tompany/BCD-0o27-3D-Printables/STL files/ANYCOLUR___bcPositionBlockRight.stl

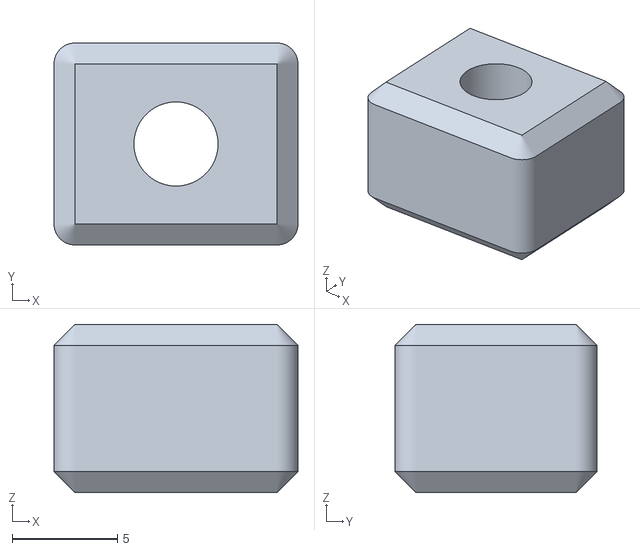
[picture p13: CAD file, 2023-10-08]
STL files/ANYCOLUR___bcPositionBlockRight.stl
11.6 x 9.60 x 8.00
