tompany/BCD-0o27-3D-Printables/STL files/RED___bmRedButtonB.stl

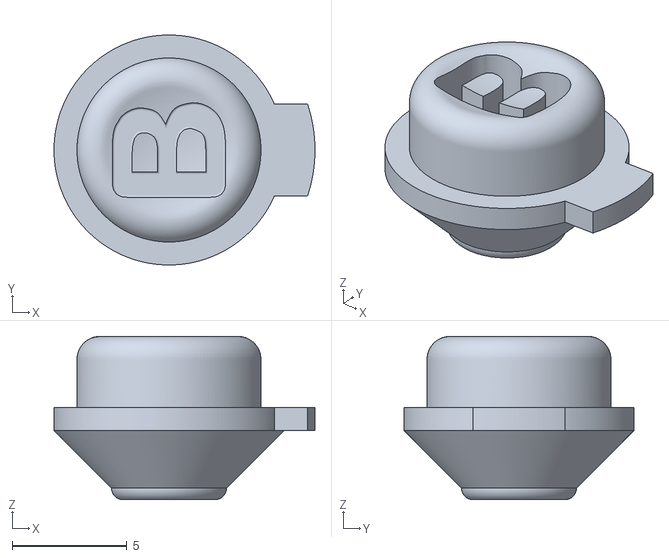
[picture p14: CAD file, 2023-10-08]
STL files/RED___bmRedButtonB.stl
11.3 x 10.00 x 7.10
