tompany/BCD-0o27-3D-Printables/STL files/BLACK___bmBlackButtonLeverW.stl

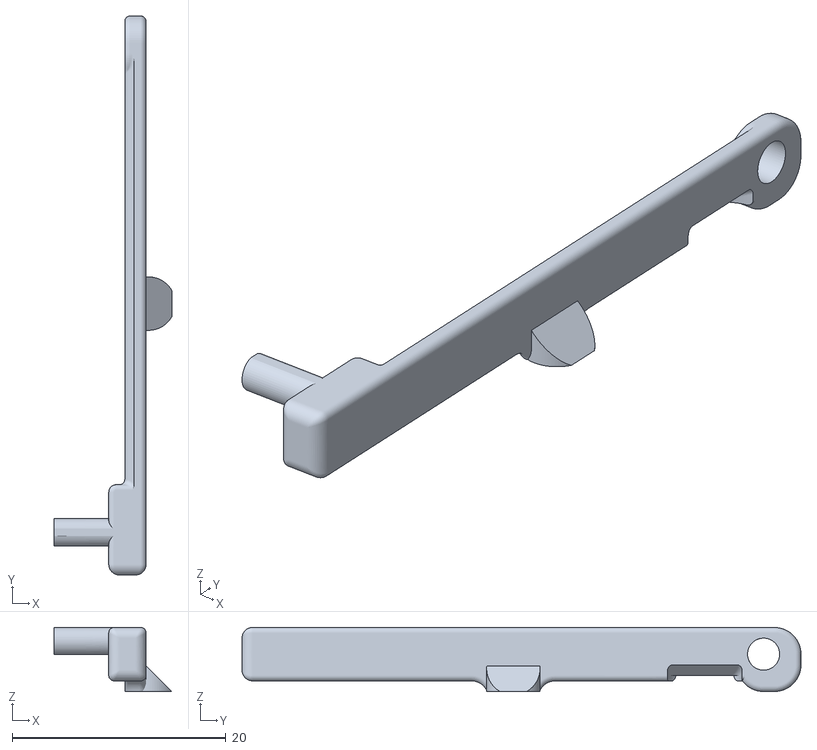
[picture p15: CAD file, 2023-10-08]
STL files/BLACK___bmBlackButtonLeverW.stl
11.0 x 52.3 x 6.00
