tompany/BCD-0o27-3D-Printables/STL files/BLACK___bcSwitchCoverRight.stl

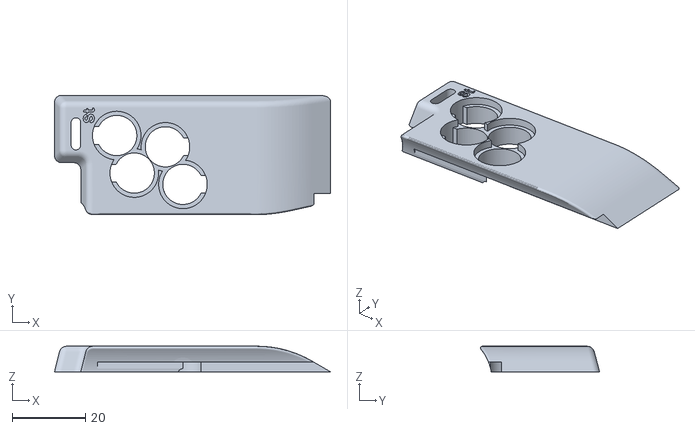
[picture p16: CAD file, 2023-10-08]
STL files/BLACK___bcSwitchCoverRight.stl
75.6 x 32.7 x 7.00
