tompany/BCD-0o27-3D-Printables/STL files/BLUE_TRANSP___bcCoverBot.stl

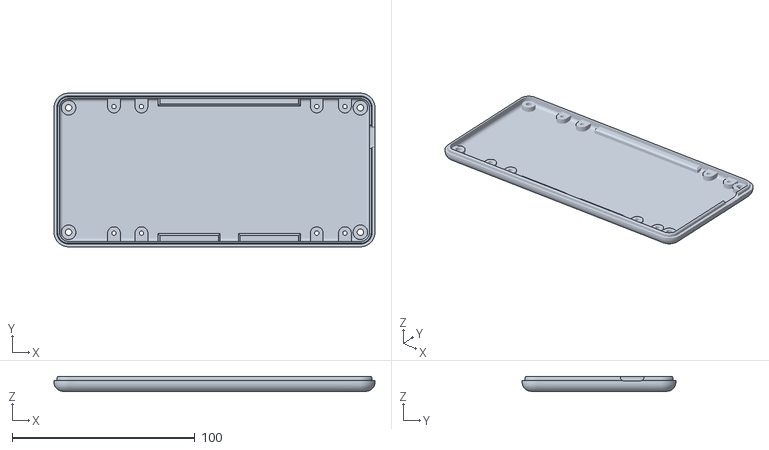
[picture p18: CAD file, 2023-10-08]
STL files/BLUE_TRANSP___bcCoverBot.stl
175.8 x 84.2 x 8.00
