tompany/BCD-0o27-3D-Printables/STL files/WHITE___bcCoverTop (FDM).stl

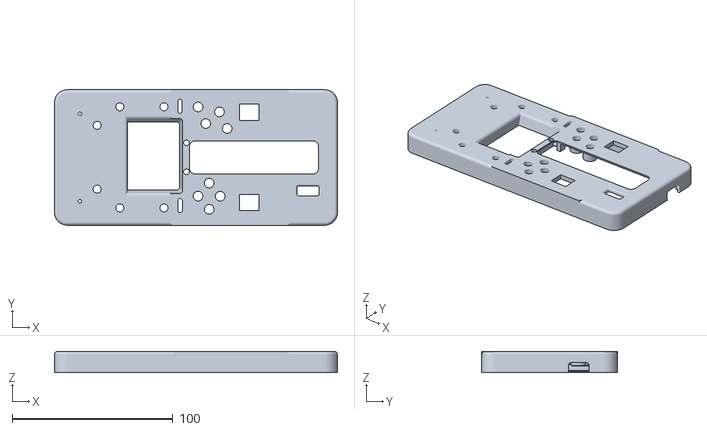
[picture p19: CAD file, 2023-10-08]
STL files/WHITE___bcCoverTop (FDM).stl
175.8 x 84.2 x 13.3
