tompany/BCD-0o27-3D-Printables/STL files/BLACK___bmOnOffButton.stl

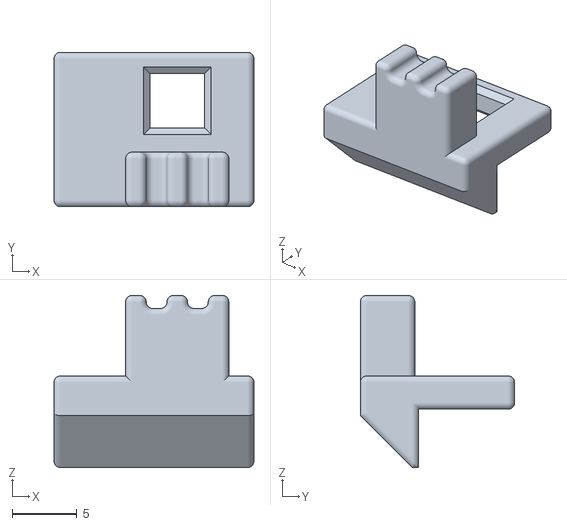
[picture p20: CAD file, 2023-10-08]
STL files/BLACK___bmOnOffButton.stl
15.4 x 11.9 x 13.2
